BtheDestroyer/rhythm-machine/src/input.cpp

#include "input.h"
#include "pico/stdlib.h"   // stdlib

Button::Button(std::uint32_t gpio_pin)
    : gpio_pin{ gpio_pin }
{
    gpio_set_dir(gpio_pin, GPIO_IN);
    gpio_set_pulls(gpio_pin, true, false);
}

void Button::update()
{
    const bool is_pressed{ !gpio_get(gpio_pin) };

    switch (last_state)
    {
    case State::Uninitialized:
        if (is_pressed)
        {
            last_state = State::Pressed;
        }
        else
        {
            last_state = State::Open;
        }
        break;
    case State::Released:
        last_state = State::Open;
        [[fallthrough]];
    case State::Open:
        if (is_pressed)
        {
            last_state = State::Pressed;
        }
        break;
    case State::Pressed:
        last_state = State::Held;
        [[fallthrough]];
    case State::Held:
        if (!is_pressed)
        {
            last_state = State::Released;
        }
        break;
    }
}
